crice009/Arduino_Learning_Board/eagle/single-sided_v2_traces.png

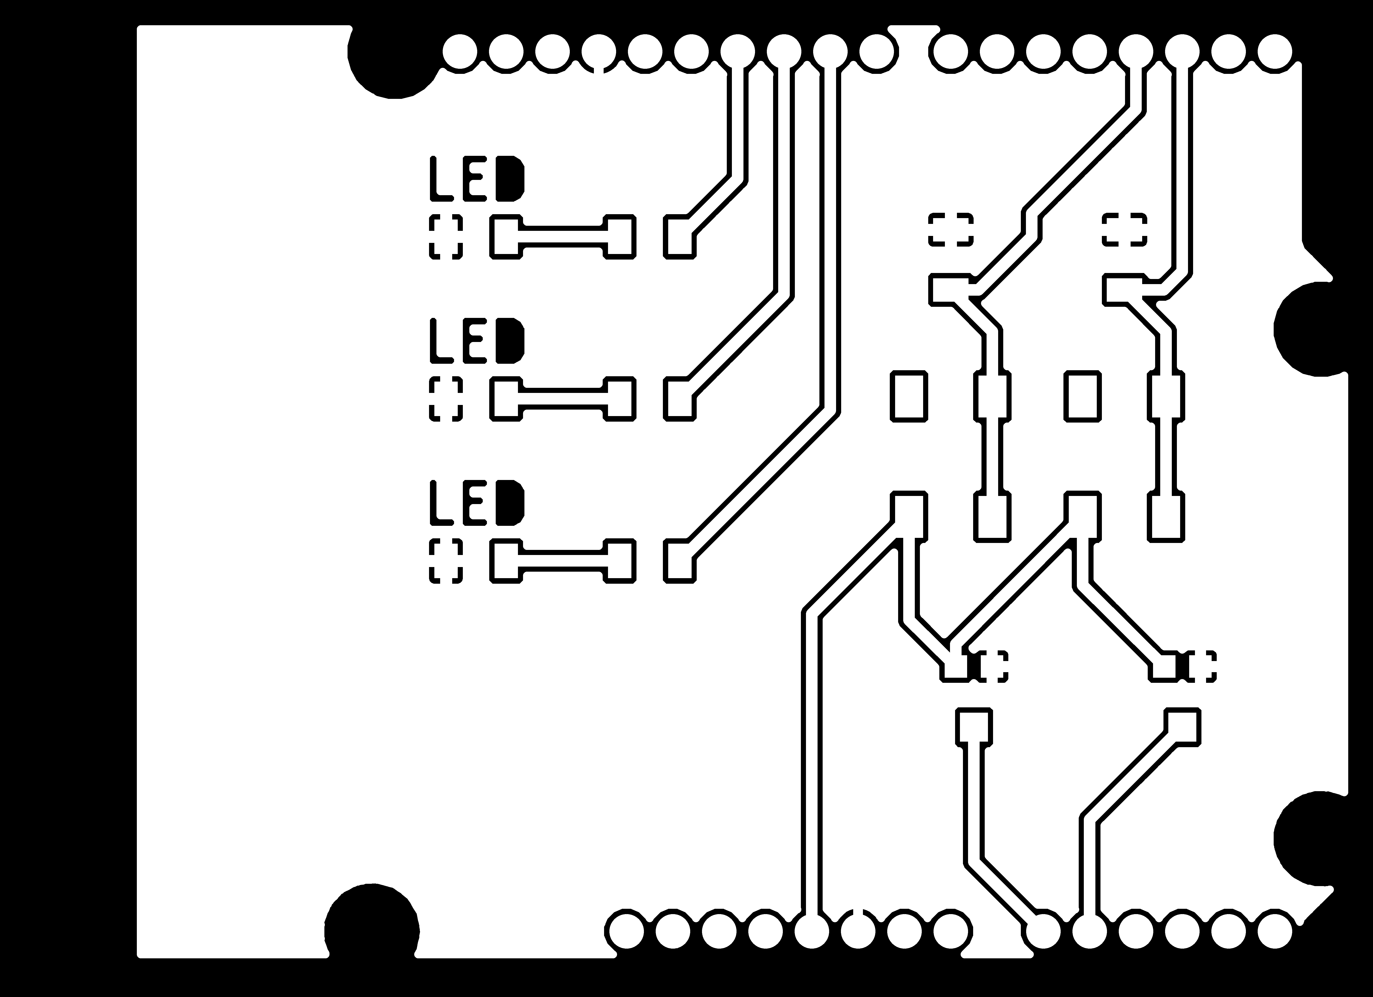
eagle/single-sided_v2_traces.png
